xsuz/Device-XNavi/src/stm32g441/Core/Src/usart.cpp

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
/* Includes ------------------------------------------------------------------*/
#include "usart.h"

/* USER CODE BEGIN 0 */

#include <SEGGER_RTT.h>

/* USER CODE END 0 */

UART_HandleTypeDef huart2;
DMA_HandleTypeDef hdma_usart2_rx;
DMA_HandleTypeDef hdma_usart2_tx;

/* USART2 init function */

void MX_USART2_UART_Init(void)
{

    huart2.Instance = USART2;
    huart2.Init.BaudRate = 115200;
    huart2.Init.WordLength = UART_WORDLENGTH_8B;
    huart2.Init.StopBits = UART_STOPBITS_1;
    huart2.Init.Parity = UART_PARITY_NONE;
    huart2.Init.Mode = UART_MODE_TX_RX;
    huart2.Init.HwFlowCtl = UART_HWCONTROL_NONE;
    huart2.Init.OverSampling = UART_OVERSAMPLING_16;
    huart2.Init.OneBitSampling = UART_ONE_BIT_SAMPLE_DISABLE;
    huart2.Init.ClockPrescaler = UART_PRESCALER_DIV1;
    huart2.AdvancedInit.AdvFeatureInit = UART_ADVFEATURE_NO_INIT;
    if (HAL_UART_Init(&huart2) != HAL_OK)
    {
        Error_Handler();
    }
    if (HAL_UARTEx_SetTxFifoThreshold(&huart2, UART_TXFIFO_THRESHOLD_1_8) != HAL_OK)
    {
        Error_Handler();
    }
    if (HAL_UARTEx_SetRxFifoThreshold(&huart2, UART_RXFIFO_THRESHOLD_1_8) != HAL_OK)
    {
        Error_Handler();
    }
    if (HAL_UARTEx_DisableFifoMode(&huart2) != HAL_OK)
    {
        Error_Handler();
    }
    /* USER CODE BEGIN USART2_Init 2 */

    HAL_UART_Receive_DMA(&huart2, uart2::RxBuff, uart2::USART_RX_BUFFSIZE);

    /* USER CODE END USART2_Init 2 */
}

void HAL_UART_MspInit(UART_HandleTypeDef *uartHandle)
{

    GPIO_InitTypeDef GPIO_InitStruct;
    RCC_PeriphCLKInitTypeDef PeriphClkInit;
    if (uartHandle->Instance == USART2)
    {
        /** Initializes the peripherals clocks
         */
        PeriphClkInit.PeriphClockSelection = RCC_PERIPHCLK_USART2;
        PeriphClkInit.Usart2ClockSelection = RCC_USART2CLKSOURCE_PCLK1;
        if (HAL_RCCEx_PeriphCLKConfig(&PeriphClkInit) != HAL_OK)
        {
            Error_Handler();
        }

        /* USART2 clock enable */
        __HAL_RCC_USART2_CLK_ENABLE();

        __HAL_RCC_GPIOA_CLK_ENABLE();
        /**USART2 GPIO Configuration
        PA2     ------> USART2_TX
        PA3     ------> USART2_RX
        */
        GPIO_InitStruct.Pin = GPIO_PIN_2 | GPIO_PIN_3;
        GPIO_InitStruct.Mode = GPIO_MODE_AF_PP;
        GPIO_InitStruct.Pull = GPIO_NOPULL;
        GPIO_InitStruct.Speed = GPIO_SPEED_FREQ_LOW;
        GPIO_InitStruct.Alternate = GPIO_AF7_USART2;
        HAL_GPIO_Init(GPIOA, &GPIO_InitStruct);

        /* USART2 DMA Init */
        /* USART2_RX Init */
        hdma_usart2_rx.Instance = DMA1_Channel1;
        hdma_usart2_rx.Init.Request = DMA_REQUEST_USART2_RX;
        hdma_usart2_rx.Init.Direction = DMA_PERIPH_TO_MEMORY;
        hdma_usart2_rx.Init.PeriphInc = DMA_PINC_DISABLE;
        hdma_usart2_rx.Init.MemInc = DMA_MINC_ENABLE;
        hdma_usart2_rx.Init.PeriphDataAlignment = DMA_PDATAALIGN_BYTE;
        hdma_usart2_rx.Init.MemDataAlignment = DMA_MDATAALIGN_BYTE;
        hdma_usart2_rx.Init.Mode = DMA_CIRCULAR;
        hdma_usart2_rx.Init.Priority = DMA_PRIORITY_HIGH;
        if (HAL_DMA_Init(&hdma_usart2_rx) != HAL_OK)
        {
            Error_Handler();
        }

        __HAL_LINKDMA(uartHandle, hdmarx, hdma_usart2_rx);

        /* USART2_TX Init */
        hdma_usart2_tx.Instance = DMA1_Channel2;
        hdma_usart2_tx.Init.Request = DMA_REQUEST_USART2_TX;
        hdma_usart2_tx.Init.Direction = DMA_MEMORY_TO_PERIPH;
        hdma_usart2_tx.Init.PeriphInc = DMA_PINC_DISABLE;
        hdma_usart2_tx.Init.MemInc = DMA_MINC_ENABLE;
        hdma_usart2_tx.Init.PeriphDataAlignment = DMA_PDATAALIGN_BYTE;
        hdma_usart2_tx.Init.MemDataAlignment = DMA_MDATAALIGN_BYTE;
        hdma_usart2_tx.Init.Mode = DMA_NORMAL;
        hdma_usart2_tx.Init.Priority = DMA_PRIORITY_LOW;
        if (HAL_DMA_Init(&hdma_usart2_tx) != HAL_OK)
        {
            Error_Handler();
        }

        __HAL_LINKDMA(uartHandle, hdmatx, hdma_usart2_tx);

        /* USART2 interrupt Init */
        HAL_NVIC_SetPriority(USART2_IRQn, 5, 0);
        HAL_NVIC_EnableIRQ(USART2_IRQn);
    }
}

void HAL_UART_MspDeInit(UART_HandleTypeDef *uartHandle)
{

    if (uartHandle->Instance == USART2)
    {
        /* Peripheral clock disable */
        __HAL_RCC_USART2_CLK_DISABLE();

        /**USART2 GPIO Configuration
        PA2     ------> USART2_TX
        PA3     ------> USART2_RX
        */
        HAL_GPIO_DeInit(GPIOA, GPIO_PIN_2 | GPIO_PIN_3);

        /* USART2 DMA DeInit */
        HAL_DMA_DeInit(uartHandle->hdmarx);
        HAL_DMA_DeInit(uartHandle->hdmatx);

        /* USART2 interrupt Deinit */
        HAL_NVIC_DisableIRQ(USART2_IRQn);
    }
}

/* USER CODE BEGIN 1 */

namespace uart2
{
    uint8_t RxBuff[USART_RX_BUFFSIZE];
    uint32_t rd_ptr;

    /// @brief Get the number of bytes available to read in the RX buffer
    /// @return Number of bytes available to read
    int available()
    {
        return ((USART_RX_BUFFSIZE - __HAL_DMA_GET_COUNTER(huart2.hdmarx)) % (USART_RX_BUFFSIZE) - rd_ptr) % USART_RX_BUFFSIZE;
    }

    /// @brief Read a byte from the RX buffer
    /// @return The byte read from the RX buffer, or 0 if no data is available
    uint8_t read()
    {
        if (available() == 0)
            return 0;
        uint8_t data = RxBuff[rd_ptr];
        rd_ptr = (rd_ptr + 1) % USART_RX_BUFFSIZE;
        return data;
    }

    /// @brief Refresh the RX buffer by resetting the read pointer and reinitializing the DMA
    void refresh()
    {
        rd_ptr = 0;
        HAL_UART_Receive_DMA(&huart2, RxBuff, USART_RX_BUFFSIZE);
    }
}

void HAL_UART_RxCpltCallback(UART_HandleTypeDef *huart)
{
    if (huart->Instance == USART2)
    {
        HAL_UART_Receive_DMA(&huart2, uart2::RxBuff, uart2::USART_RX_BUFFSIZE);
    }
}

void HAL_UART_TxCpltCallback(UART_HandleTypeDef *huart) {
    if (huart->Instance == USART2)
    {
        huart2.gState = HAL_UART_STATE_READY;
    }
}

/* USER CODE END 1 */
