xsuz/Device-XNavi/src/rp2350/src/imu.cpp

#include <FreeRTOS.h>
#include <task.h>
#include <queue.h>

#include "imu.h"

#include "madgwick.hpp"

#include "clock.h"
#include "config.hpp"

#include <SEGGER_RTT.h>
#include <mavlink/swingby/mavlink.h>

#include <ASM330LHHSensor.h>
#include <SPI.h>

namespace
{
    constexpr int SPI1_CS = 13,
                  SPI1_RX = 12,
                  SPI1_SCK = 14,
                  SPI1_TX = 15;

    constexpr int delta_t = 4;

    ASM330LHHSensor asm330lhh(&SPI1, SPI1_CS, 1000000); // SPI1, CS pin 13, SPI speed 1MHz
    volatile uint32_t imu_queue_overflow = 0;
    float quat[4] = {1.0f, 0.0f, 0.0f, 0.0f};
    constexpr float deg2rad = M_PI / 180.0f;
    constexpr float acc_sensitivity = ASM330LHH_ACC_SENSITIVITY_FS_2G * 0.00980665f;            // mm/s^2
    constexpr float gyro_sensitivity = ASM330LHH_GYRO_SENSITIVITY_FS_125DPS * 0.001f * deg2rad; // mrad/s
}

void IMUTask::run()
{
    int64_t utc;
    mavlink_message_t msg;
    mavlink_imu_t imu_msg;
    uint8_t count = 0;

    log_info("IMU task started.\n");

    log_info("Initializing SPI1 with RX: %d, CS: %d, SCK: %d, TX: %d\n", SPI1_RX, SPI1_CS, SPI1_SCK, SPI1_TX);
    // IMU setup
    SPI1.setRX(SPI1_RX);
    SPI1.setCS(SPI1_CS);
    SPI1.setSCK(SPI1_SCK);
    SPI1.setTX(SPI1_TX);
    SPI1.begin();
    log_info("SPI1 initialized.\n");

    if (asm330lhh.begin() == ASM330LHH_OK)
    {
        log_info("ASM330LHH initialized successfully\n");
    }
    else
    {
        log_error("Failed to initialize ASM330LHH\n");
        while (1)
            ; // Halt if initialization fails
    }
    asm330lhh.Enable_X();
    asm330lhh.Enable_G();

    asm330lhh.Set_X_FS(ASM330LHH_2g);
    asm330lhh.Set_G_FS(ASM330LHH_125dps);

    log_info("ASM330LHH enabled for accelerometer and gyroscope.\n");

    TickType_t last_wake_time = xTaskGetTickCount();
    while (1)
    {
        vTaskDelayUntil(&last_wake_time, delta_t);

        utc = sys_clock::get_timestamp();
        int16_t acc[3], gyr[3];
        asm330lhh.Get_X_AxesRaw(acc);
        asm330lhh.Get_G_AxesRaw(gyr);
        imu_msg.time_boot_ms = millis();
        imu_msg.xacc = float(acc[0]) * acc_sensitivity;   // a_x(m/s^2)
        imu_msg.yacc = float(acc[1]) * acc_sensitivity;   // a_y(m/s^2)
        imu_msg.zacc = float(acc[2]) * acc_sensitivity;   // a_z(m/s^2)
        imu_msg.xgyro = float(gyr[0]) * gyro_sensitivity; // // w_x(rad/s)
        imu_msg.ygyro = float(gyr[1]) * gyro_sensitivity; // // w_y(rad/s)
        imu_msg.zgyro = float(gyr[2]) * gyro_sensitivity; // // w_z(rad/s)

        mavlink_msg_imu_encode(config::mavlink::system_id, config::mavlink::component_id, &msg, &imu_msg);
        _publisher.publish(msg, utc);
    }
}
